wizzdev-pl/-pcb-esp-opto-prog/Doc/EspOptoProg HV2 220111/EspOptoProg HV2 220111 Images/14.jpg

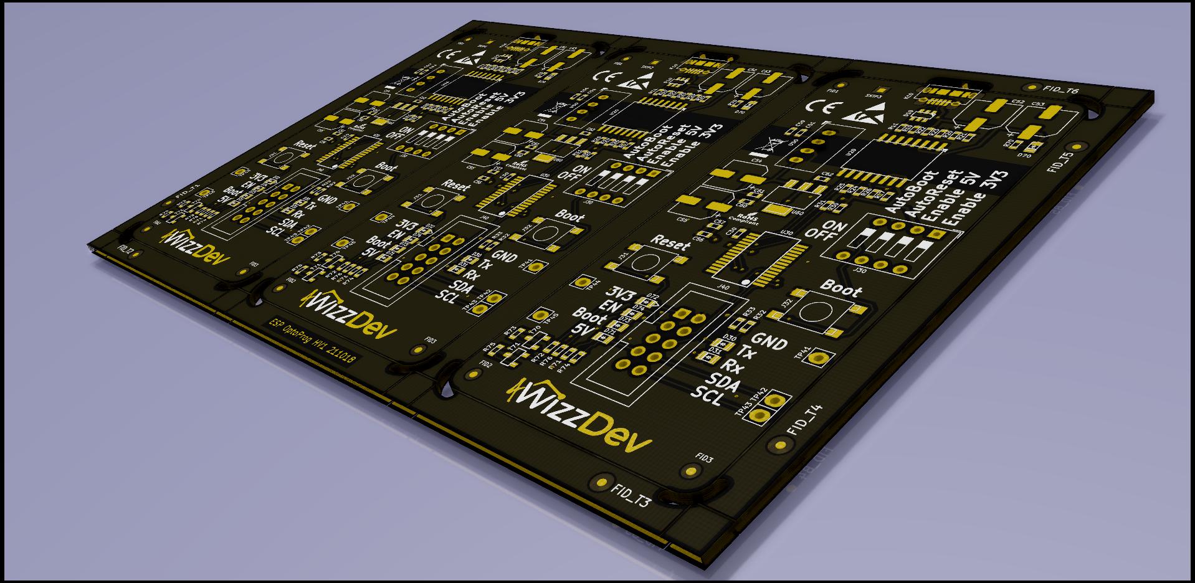
Doc/EspOptoProg HV2 220111/EspOptoProg HV2 220111 Images/14.jpg
